drdurczok/3DPrinter/CAD/StencilParts/HotEnd.fcstd

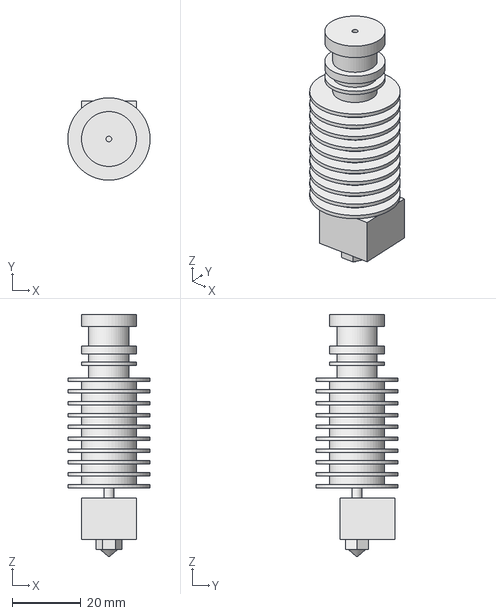
[picture p20: CAD file, 2017-04-10]
CAD/StencilParts/HotEnd.fcstd
24.0 x 24.0 x 70.5 mm
