drdurczok/3DPrinter/CAD/TopFrame/Corner_Bottom.fcstd

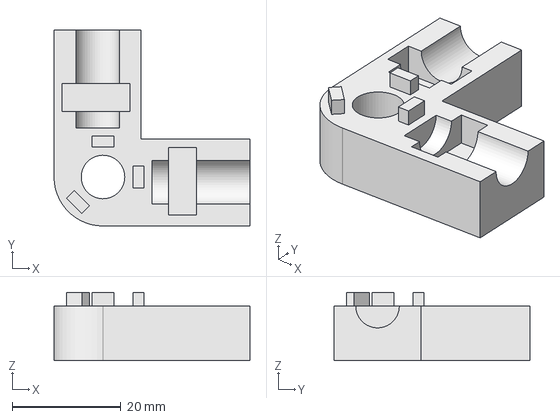
[picture p21: CAD file, 2017-05-19]
CAD/TopFrame/Corner_Bottom.fcstd
36.0 x 36.0 x 12.5 mm
