drdurczok/3DPrinter/CAD/X-Axis/HotEndMount.fcstd

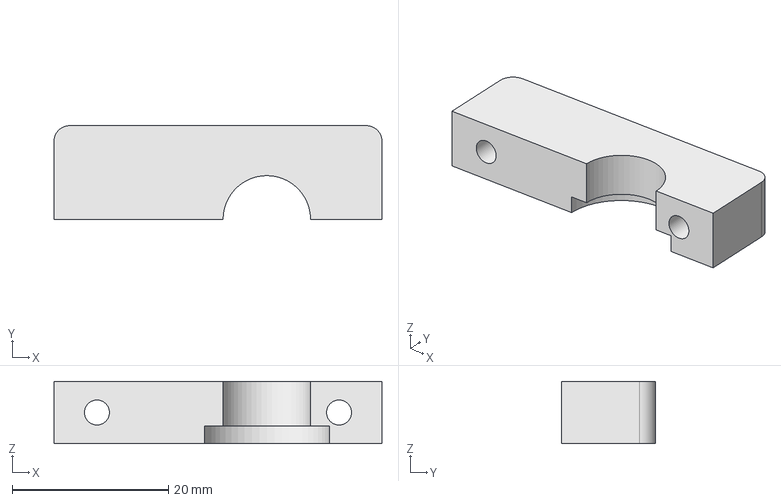
[picture p22: CAD file, 2017-05-19]
CAD/X-Axis/HotEndMount.fcstd
42.0 x 12.0 x 8.00 mm
