drdurczok/3DPrinter/CAD/Y-Axis/Y_MotorMount.fcstd

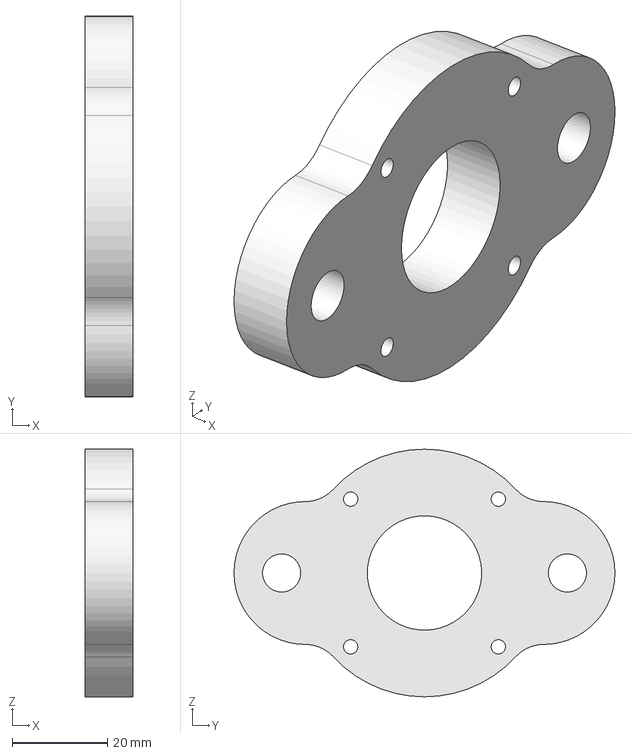
[picture p23: CAD file, 2017-05-19]
CAD/Y-Axis/Y_MotorMount.fcstd
10.0 x 80.0 x 52.0 mm
