drdurczok/3DPrinter/CAD/Z-Axis/Z-Axis_AxisMount.fcstd

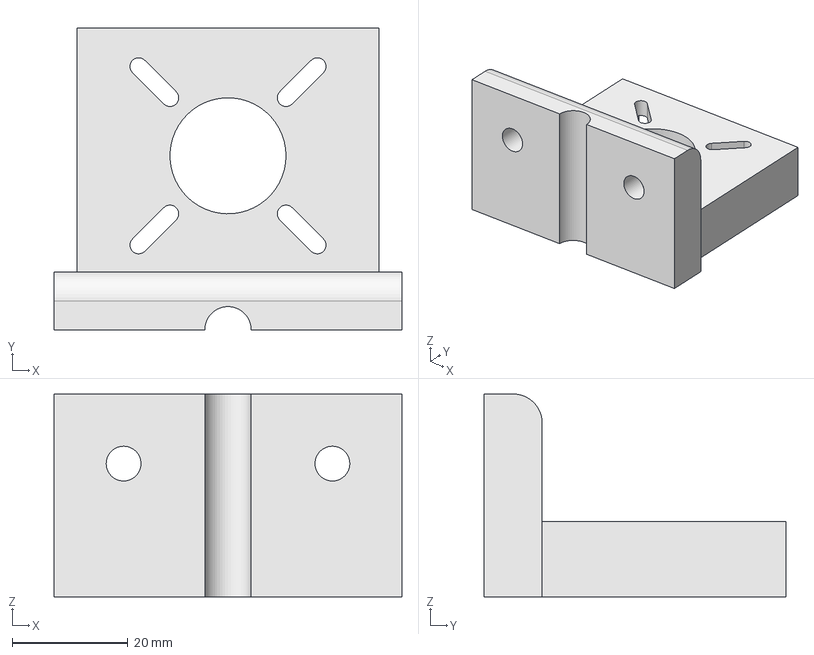
[picture p24: CAD file, 2017-04-15]
CAD/Z-Axis/Z-Axis_AxisMount.fcstd
60.0 x 52.0 x 35.0 mm
