drdurczok/3DPrinter/CAD/BottemFrame/board_shelf.fcstd

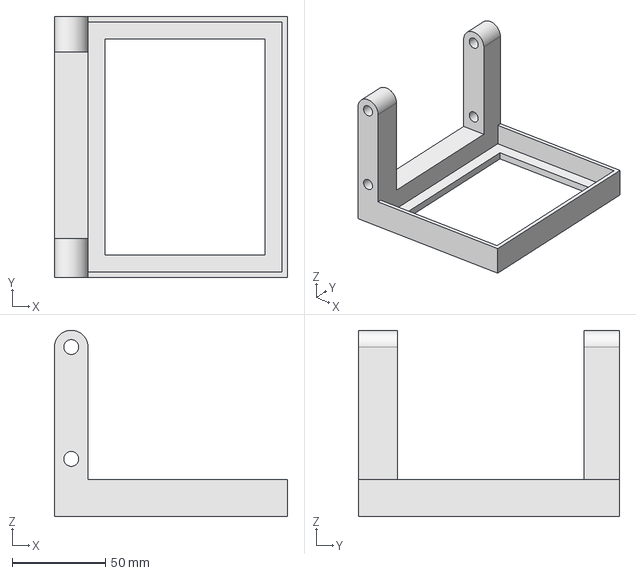
[picture p25: CAD file, 2017-05-19]
CAD/BottemFrame/board_shelf.fcstd
125.0 x 140.0 x 100.0 mm
