drdurczok/3DPrinter/CAD/PrintingBed/SGB_BearingMounts.fcstd

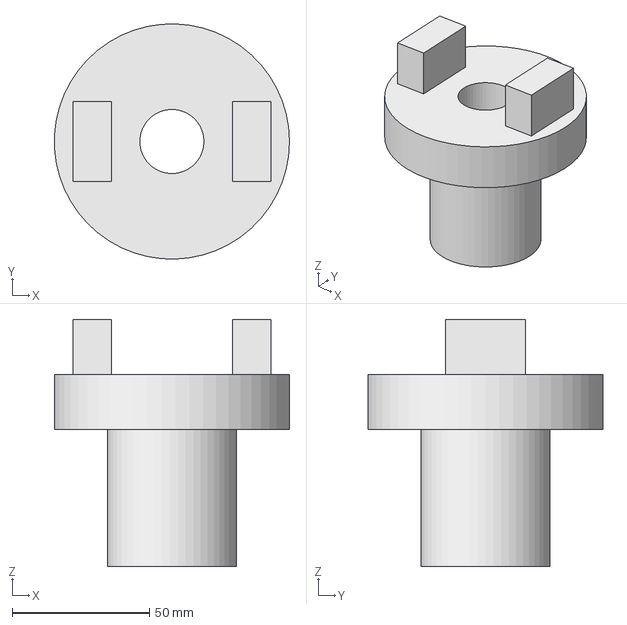
[picture p26: CAD file, 2017-03-07]
CAD/PrintingBed/SGB_BearingMounts.fcstd
85.5 x 85.6 x 90.0 mm
