drdurczok/3DPrinter/CAD/StencilParts/Nema17.fcstd

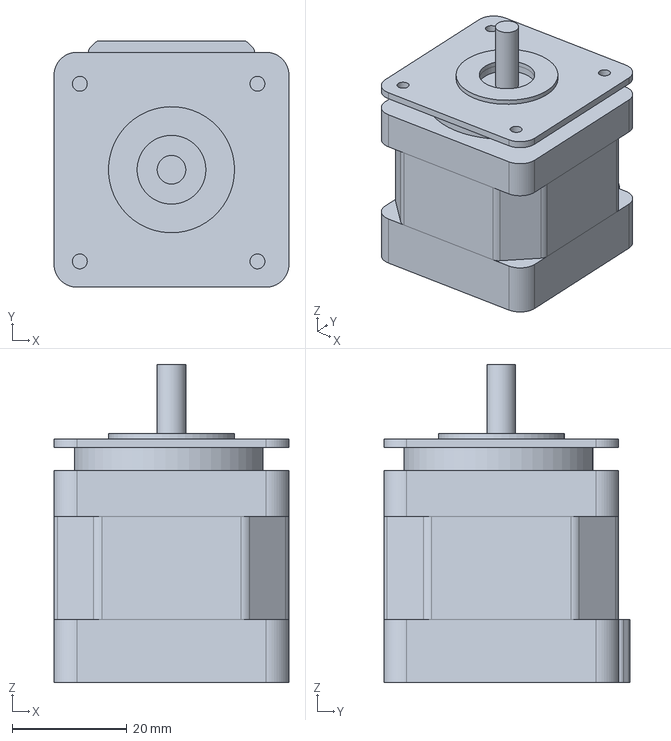
[picture p27: CAD file, 2017-04-10]
CAD/StencilParts/Nema17.fcstd
41.0 x 43.0 x 55.5 mm
