drdurczok/3DPrinter/CAD/TopFrame/Corner_Top.fcstd

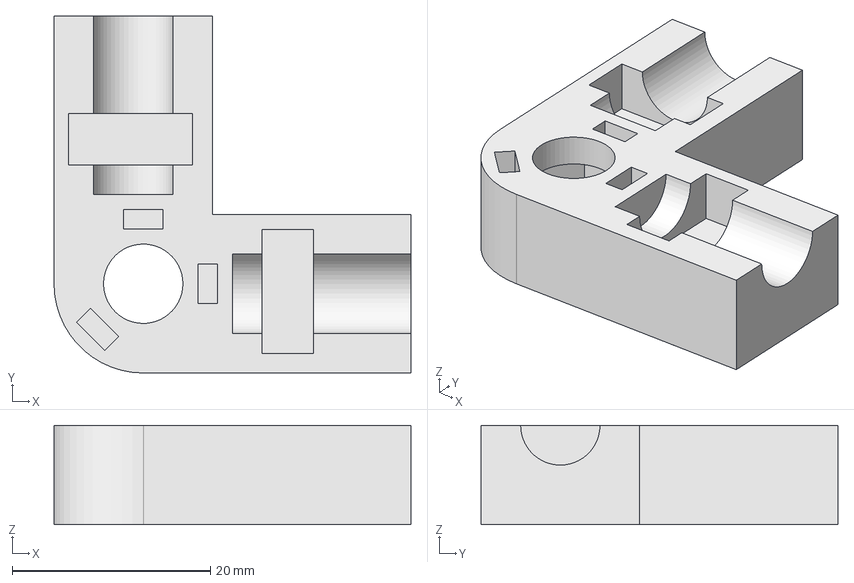
[picture p28: CAD file, 2017-05-19]
CAD/TopFrame/Corner_Top.fcstd
36.0 x 36.0 x 10.0 mm
