drdurczok/3DPrinter/CAD/X-Axis.fcstd

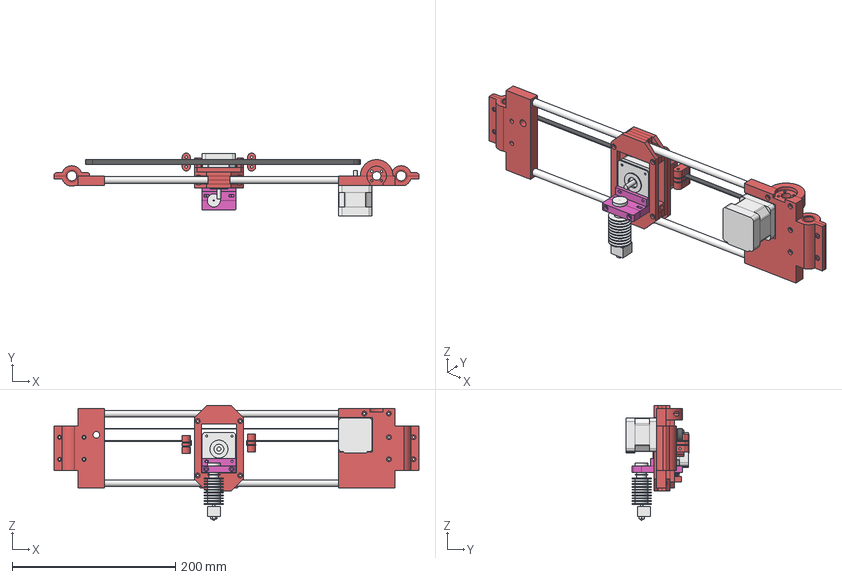
[picture p29: CAD file, 2017-05-19]
CAD/X-Axis.fcstd
446.7 x 77.0 x 141.0 mm
Nema17
Nema17_X
Belt
Spring
HotEnd
X-Rods
Shoulders
HotEndMount001
X-Carrage
