drdurczok/3DPrinter/CAD/X-Axis/X-Carrage_Back.fcstd

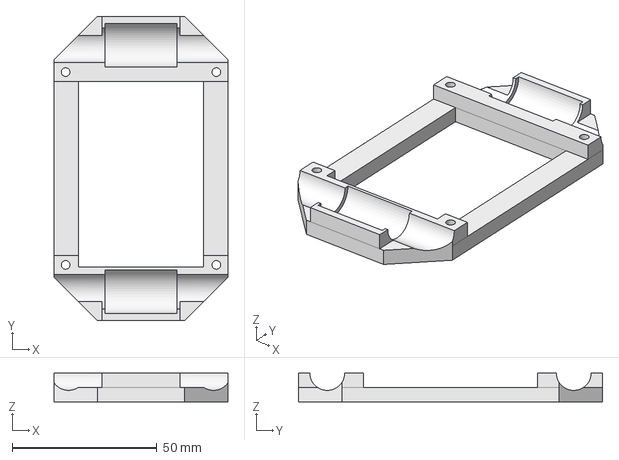
[picture p30: CAD file, 2017-05-19]
CAD/X-Axis/X-Carrage_Back.fcstd
60.0 x 105.0 x 10.0 mm
