drdurczok/3DPrinter/CAD/Y-Axis/HeightKnob.fcstd

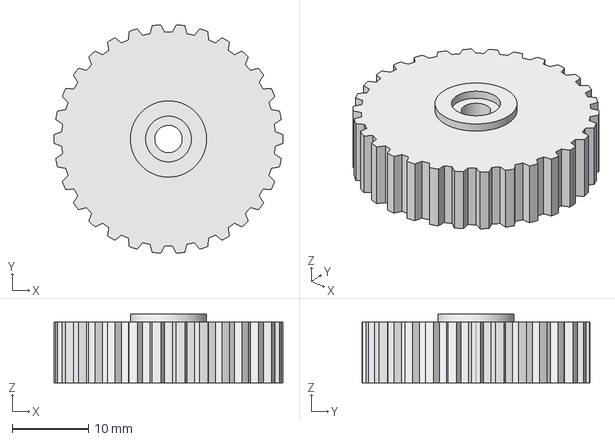
[picture p31: CAD file, 2017-04-24]
CAD/Y-Axis/HeightKnob.fcstd
30.0 x 29.9 x 9.00 mm
