drdurczok/3DPrinter/CAD/Z-Axis/Z-Axis_FrameMount.fcstd

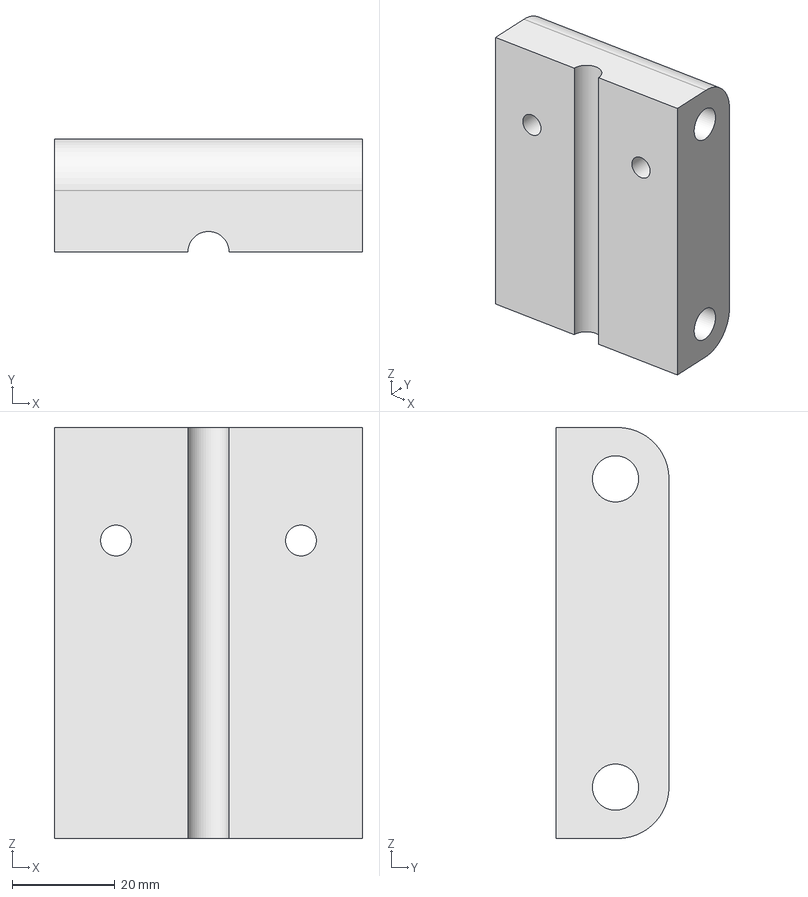
[picture p32: CAD file, 2017-04-15]
CAD/Z-Axis/Z-Axis_FrameMount.fcstd
60.0 x 22.0 x 80.0 mm
