drdurczok/3DPrinter/CAD/PrintingBed/ServoGearBox.fcstd

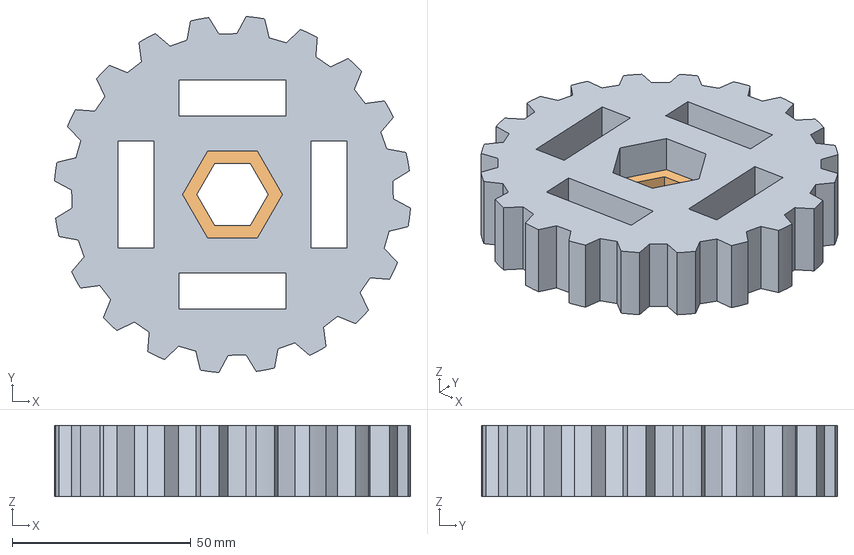
[picture p33: CAD file, 2017-03-07]
CAD/PrintingBed/ServoGearBox.fcstd
99.7 x 99.7 x 20.0 mm
NutPad
NutBreak
