drdurczok/3DPrinter/CAD/StencilParts/SmoothRod380mm.fcstd

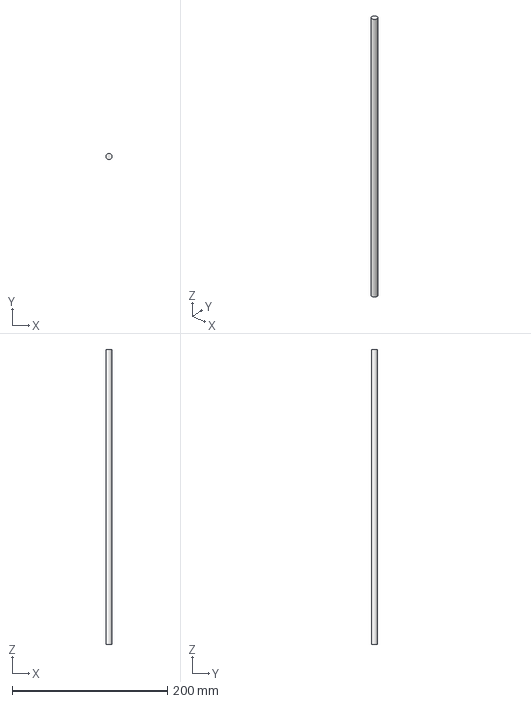
[picture p34: CAD file, 2017-04-02]
CAD/StencilParts/SmoothRod380mm.fcstd
7.99 x 8.00 x 380.0 mm
