drdurczok/3DPrinter/CAD/STP/Peripheral.step

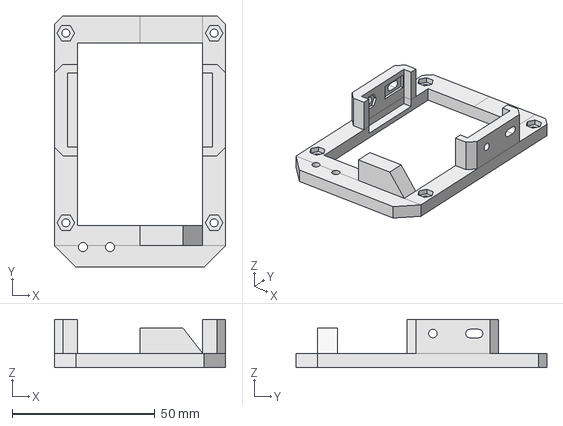
[picture p35: CAD file, 2017-05-19]
CAD/STP/Peripheral.step
60.0 x 88.0 x 17.0 mm
