drdurczok/3DPrinter/CAD/Y-Axis.fcstd

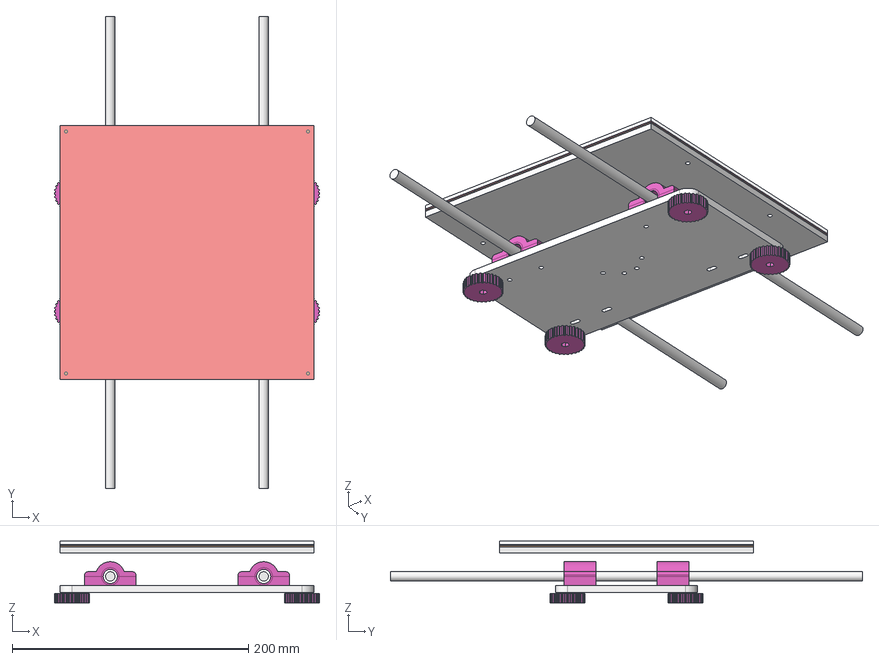
[picture p36: CAD file, 2017-04-24]
CAD/Y-Axis.fcstd
225.0 x 400.0 x 52.5 mm
Rods
Y-Base
BearingMount
PrintingBedBase
Insulation
HeatBed
GlassPrintingBed
HeightKnob
