drdurczok/3DPrinter/CAD/Y-Axis/SingleLinearBearingBASE.fcstd

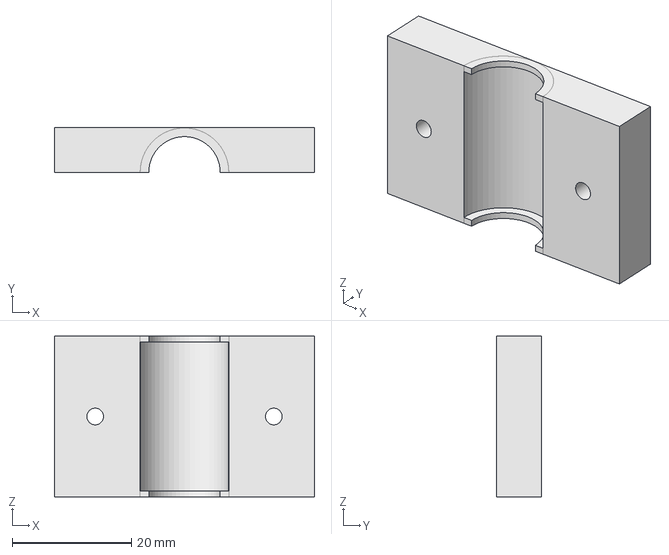
[picture p37: CAD file, 2017-04-24]
CAD/Y-Axis/SingleLinearBearingBASE.fcstd
43.7 x 7.50 x 27.0 mm
