drdurczok/3DPrinter/CAD/Frame.fcstd

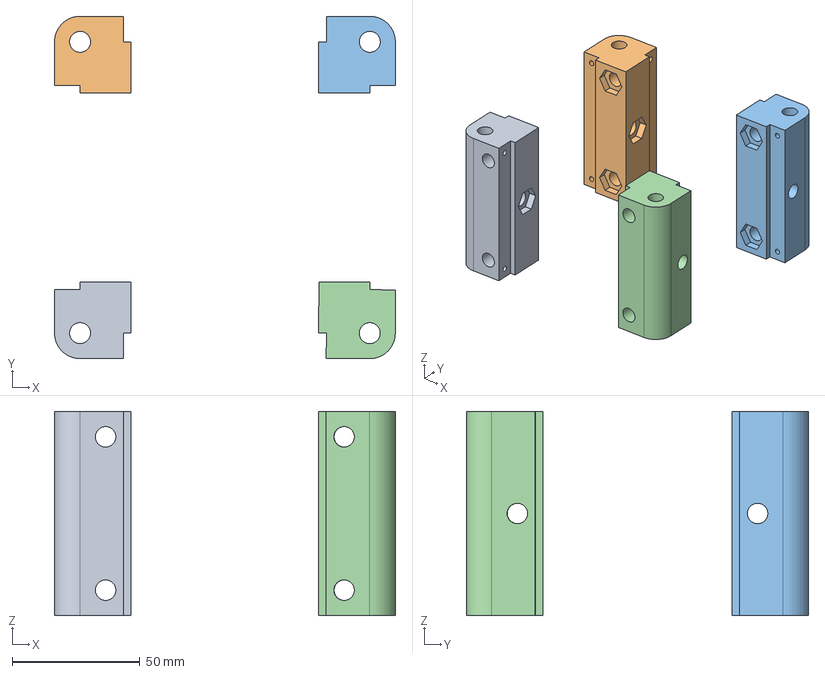
[picture p38: CAD file, 2017-04-10]
CAD/Frame.fcstd
133.4 x 134.0 x 80.0 mm
Corner_FL
Corner_BL
Corner_BR
Corner_FR
