drdurczok/3DPrinter/CAD/PrintingBed/SGH_BearingCup.fcstd

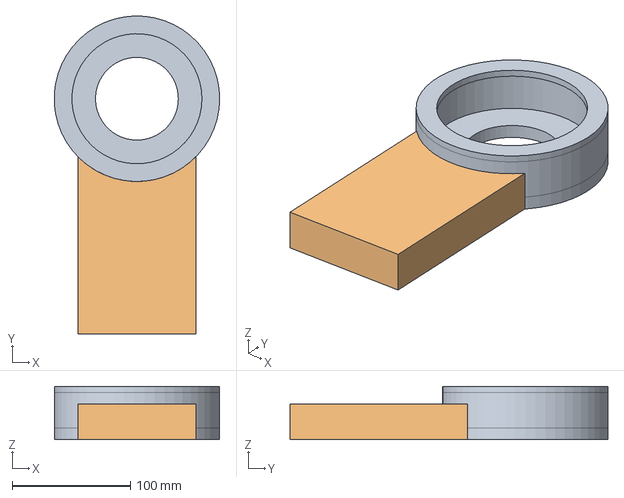
[picture p39: CAD file, 2017-03-07]
CAD/PrintingBed/SGH_BearingCup.fcstd
139.9 x 269.0 x 45.0 mm
BLock
BArm
