drdurczok/3DPrinter/CAD/StencilParts/SmoothRod406mm.fcstd

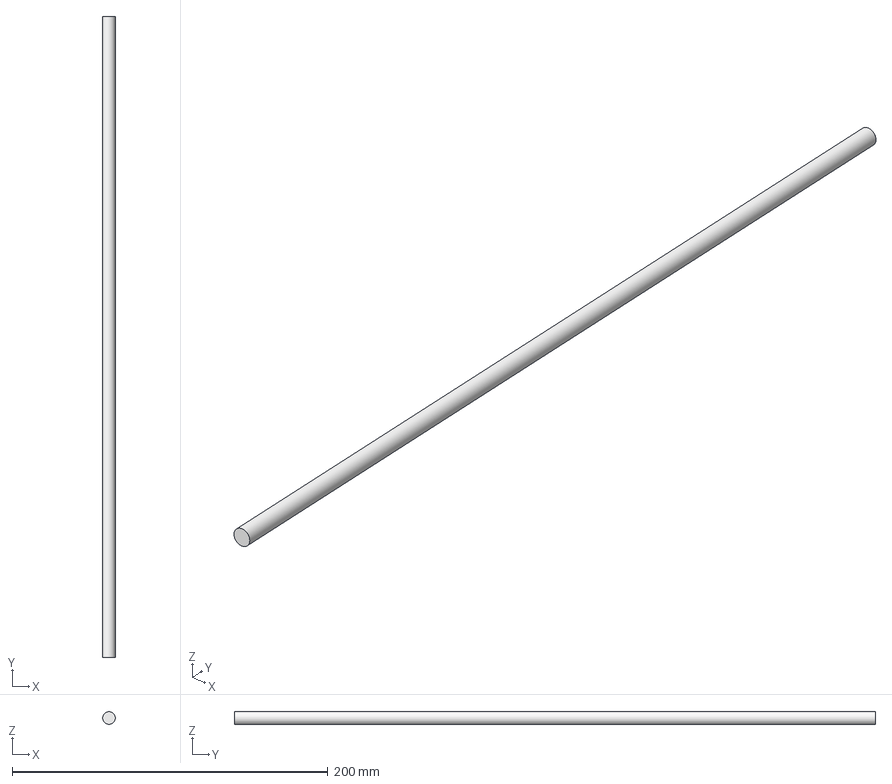
[picture p40: CAD file, 2017-04-02]
CAD/StencilParts/SmoothRod406mm.fcstd
7.99 x 406.0 x 8.00 mm
