drdurczok/3DPrinter/CAD/STP/ExtruderLever.step

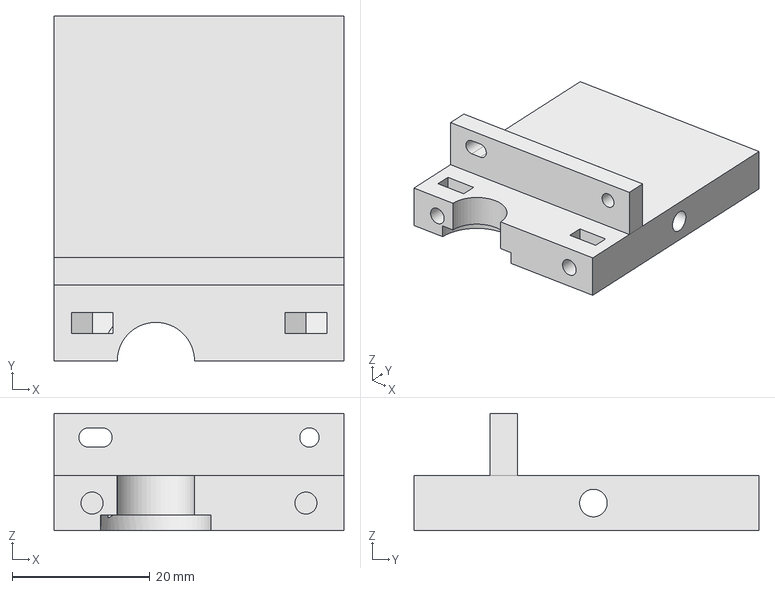
[picture p41: CAD file, 2017-05-19]
CAD/STP/ExtruderLever.step
42.0 x 50.0 x 17.0 mm
