drdurczok/3DPrinter/CAD/X-Axis/LeftShoulder.fcstd

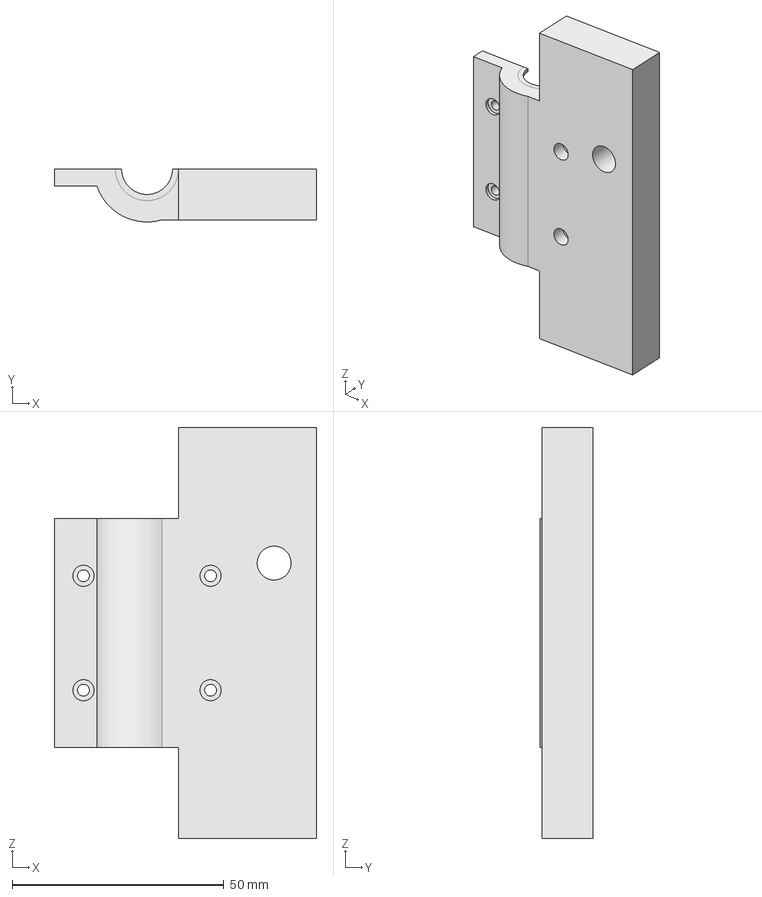
[picture p42: CAD file, 2017-05-19]
CAD/X-Axis/LeftShoulder.fcstd
61.8 x 12.5 x 97.0 mm
