drdurczok/3DPrinter/CAD/Y-Axis/SingleLinearBearingMount.fcstd

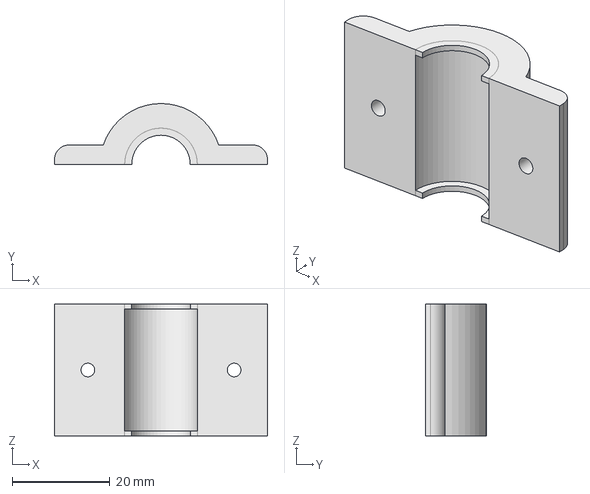
[picture p43: CAD file, 2017-04-24]
CAD/Y-Axis/SingleLinearBearingMount.fcstd
43.7 x 12.5 x 27.0 mm
