drdurczok/3DPrinter/CAD/StencilParts/SmoothRod310mm.fcstd

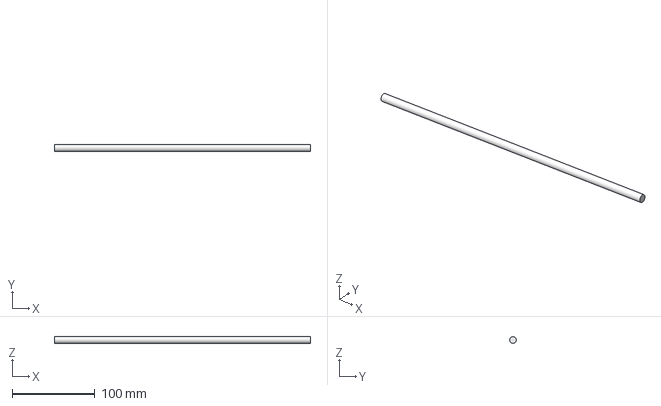
[picture p44: CAD file, 2017-04-02]
CAD/StencilParts/SmoothRod310mm.fcstd
310.0 x 7.99 x 8.00 mm
