drdurczok/3DPrinter/CAD/Y-Axis/BeltMount.fcstd

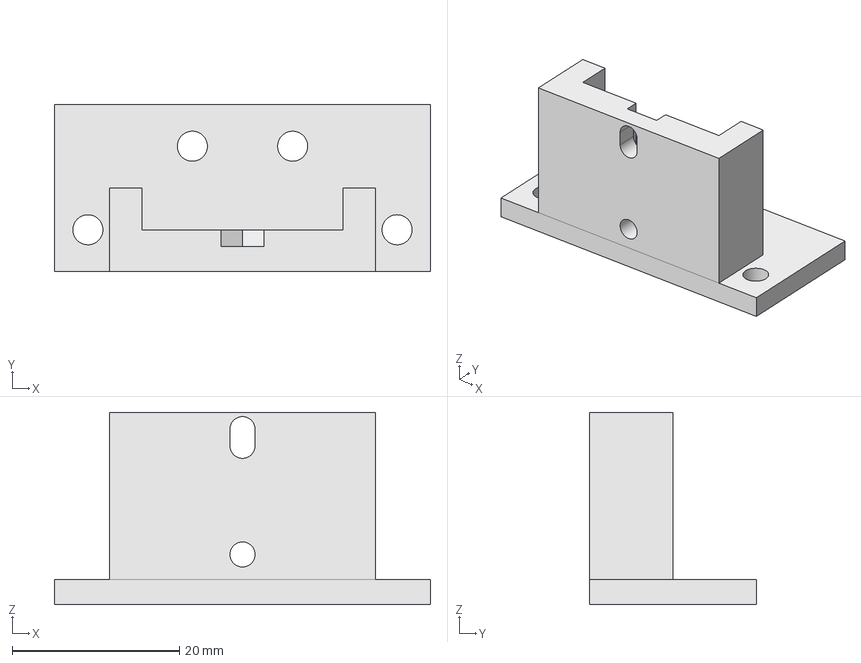
[picture p45: CAD file, 2017-04-24]
CAD/Y-Axis/BeltMount.fcstd
45.0 x 20.0 x 23.0 mm
