drdurczok/3DPrinter/CAD/StencilParts/BearingLodge.fcstd

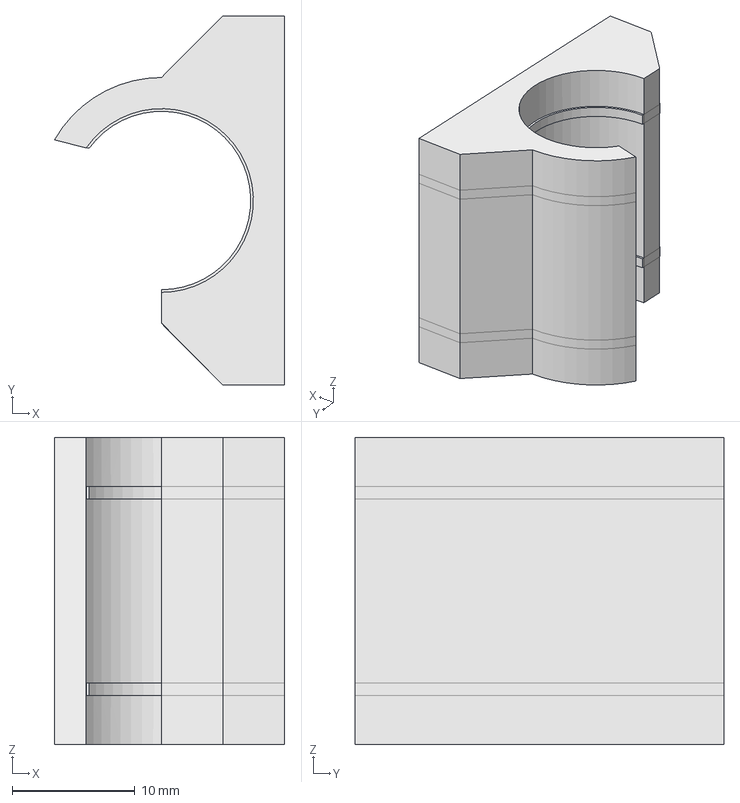
[picture p46: CAD file, 2017-03-17]
CAD/StencilParts/BearingLodge.fcstd
18.7 x 30.0 x 25.0 mm
