drdurczok/3DPrinter/CAD/Y-Axis/Y-Base.fcstd

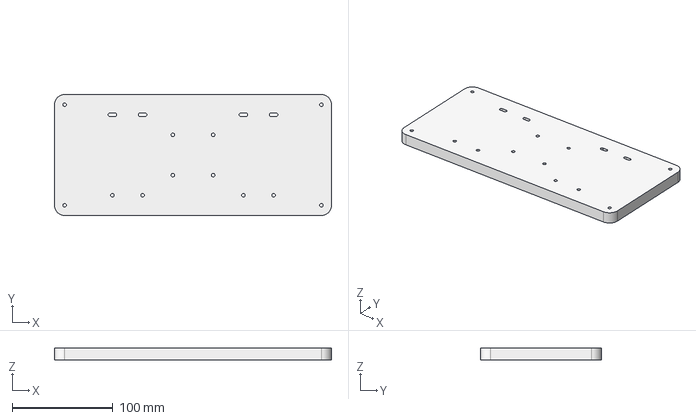
[picture p47: CAD file, 2017-04-24]
CAD/Y-Axis/Y-Base.fcstd
275.0 x 120.0 x 12.0 mm
