drdurczok/3DPrinter/CAD/X-Axis/BeltTensioner.fcstd

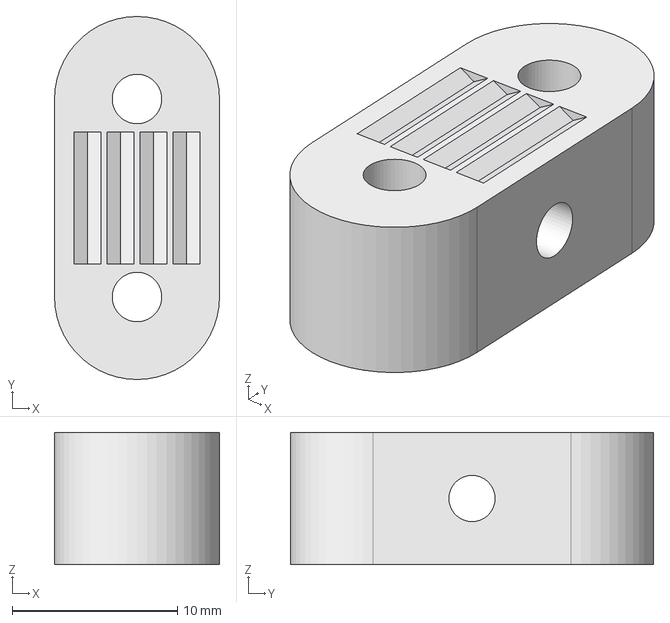
[picture p48: CAD file, 2017-04-10]
CAD/X-Axis/BeltTensioner.fcstd
10.0 x 22.0 x 8.00 mm
