drdurczok/3DPrinter/CAD/X-Axis/DoubleLinearBearingMount.fcstd

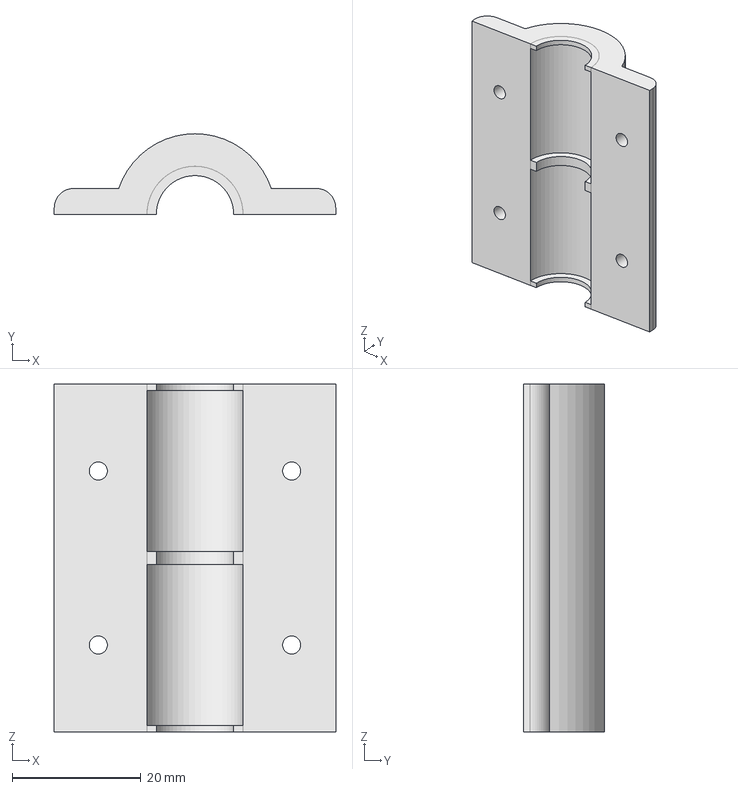
[picture p49: CAD file, 2017-04-10]
CAD/X-Axis/DoubleLinearBearingMount.fcstd
43.7 x 12.5 x 54.0 mm
