drdurczok/3DPrinter/CAD/X-Axis/BeltClip.fcstd

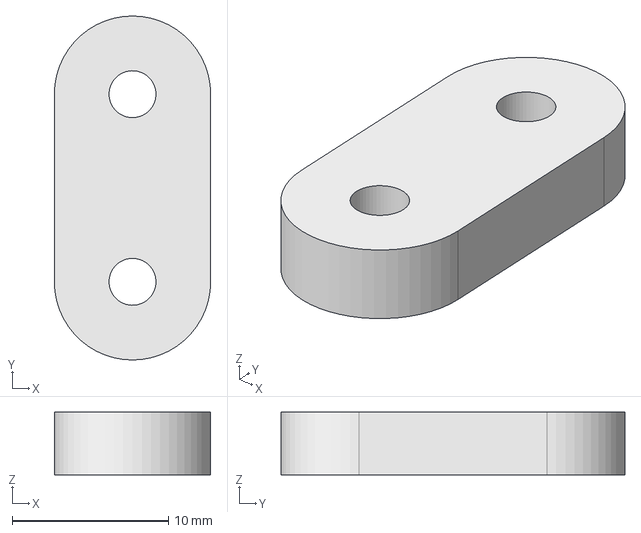
[picture p50: CAD file, 2017-04-10]
CAD/X-Axis/BeltClip.fcstd
10.0 x 22.0 x 4.00 mm
