drdurczok/3DPrinter/Technical Drawings/PDF/RightShoulder_A.pdf

# Ra3.2Ra5

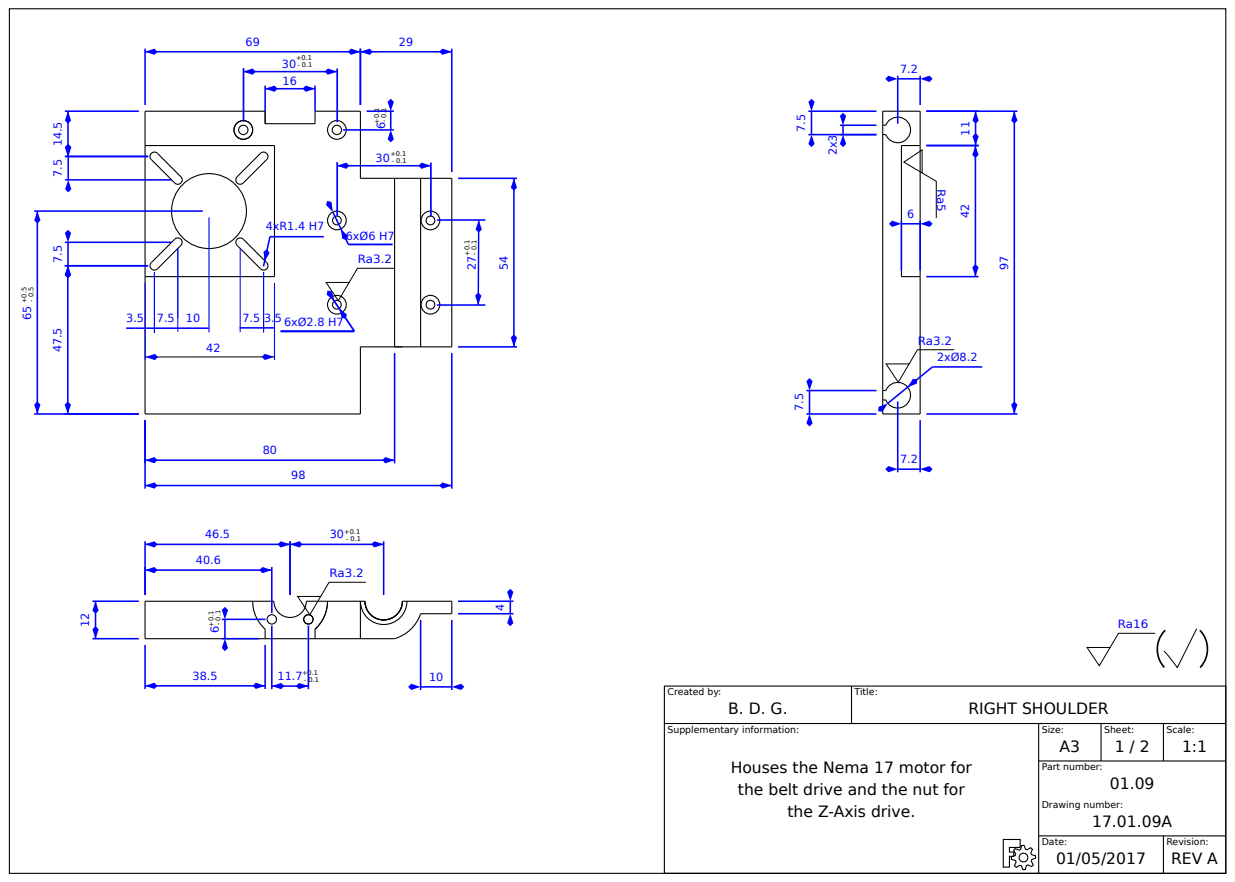
[picture p61: page 1]
Created by:; Title:; Supplementary information:; Size:; Sheet:; Scale:; Part number:; Drawing number:; Date:; Revision:; RIGHT SHOULDER; REV A

Houses the Nema 17 motor for
the belt drive and the nut for
the Z-Axis drive.
