drdurczok/3DPrinter/Technical Drawings/PDF/X-Axis.pdf

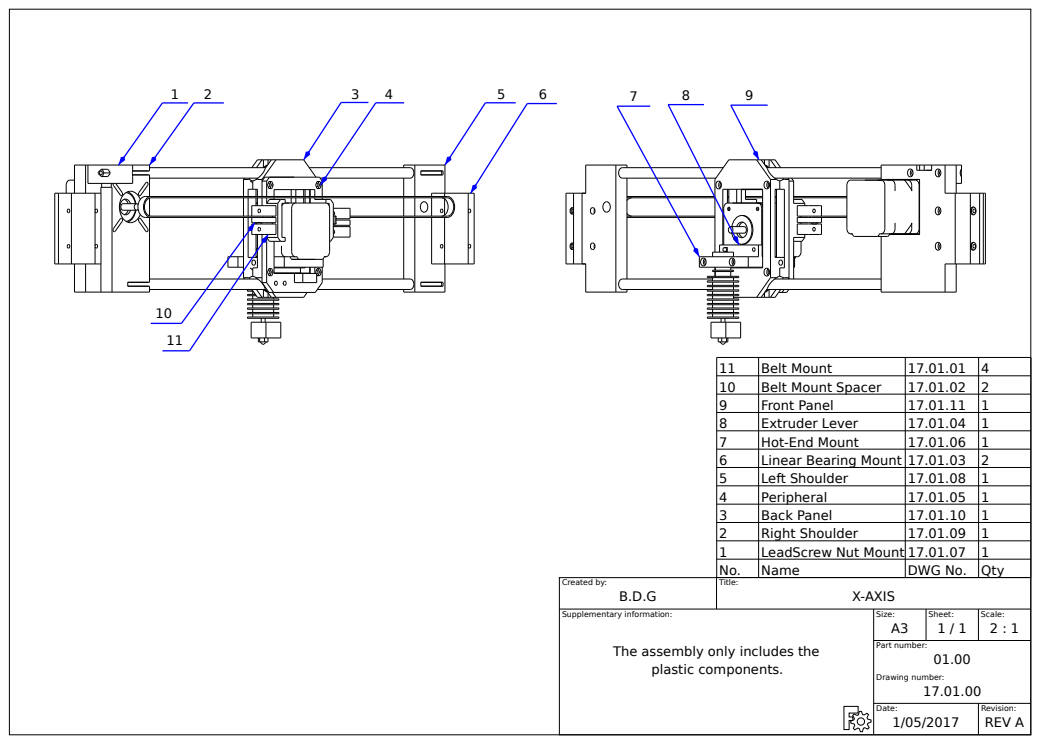
[picture p62: page 1]
Created by:; Title:; Supplementary information:; Size:; Sheet:; Scale:; Part number:; Drawing number:; Date:; Revision:; X-AXIS; REV A

11 | Belt Mount | 17.01.01 | 4
10 | Belt Mount Spacer | 17.01.02 | 2
9 | Front Panel | 17.01.11 | 1
8 | Extruder Lever | 17.01.04 | 1
7 | Hot-End Mount | 17.01.06 | 1
6 | Linear Bearing Mount | 17.01.03 | 2
5 | Left Shoulder | 17.01.08 | 1
4 | Peripheral | 17.01.05 | 1
3 | Back Panel | 17.01.10 | 1
2 | Right Shoulder | 17.01.09 | 1
1 | LeadScrew Nut Mount 17.01.07 | | 1
No. | Name | DWG No. | Qty

The assembly only includes the
plastic components.
