drdurczok/3DPrinter/Technical Drawings/PDF/X-Carrage(Back).pdf

## Ra5Ra5

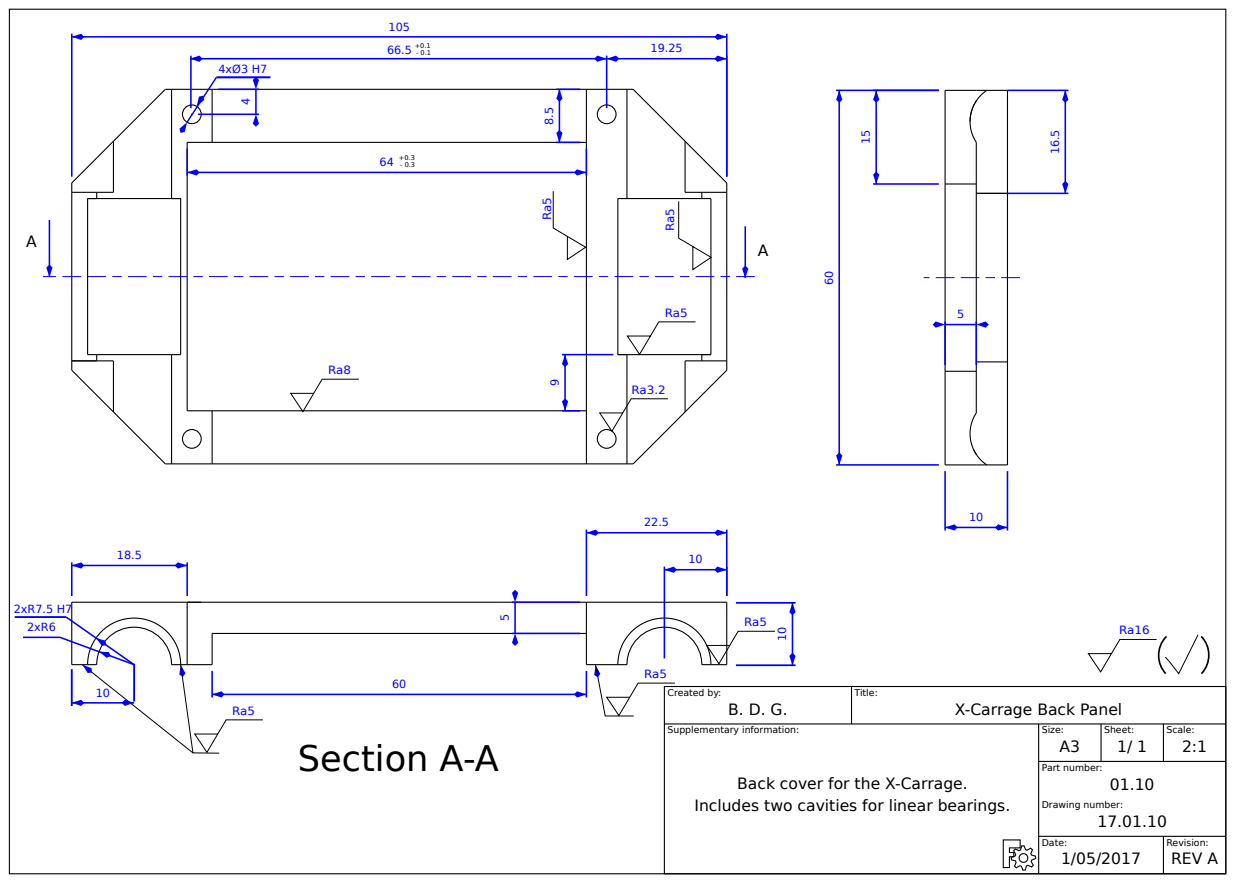
[picture p63: page 1]
Created by:; Title:; Supplementary information:; Size:; Sheet:; Scale:; Part number:; Drawing number:; Date:; Revision:; X-Carrage Back Panel; REV A; Section A-A

Back cover for the X-Carrage.
Includes two cavities for linear bearings.
