drdurczok/3DPrinter/Technical Drawings/PDF/X-Carrage(Front).pdf

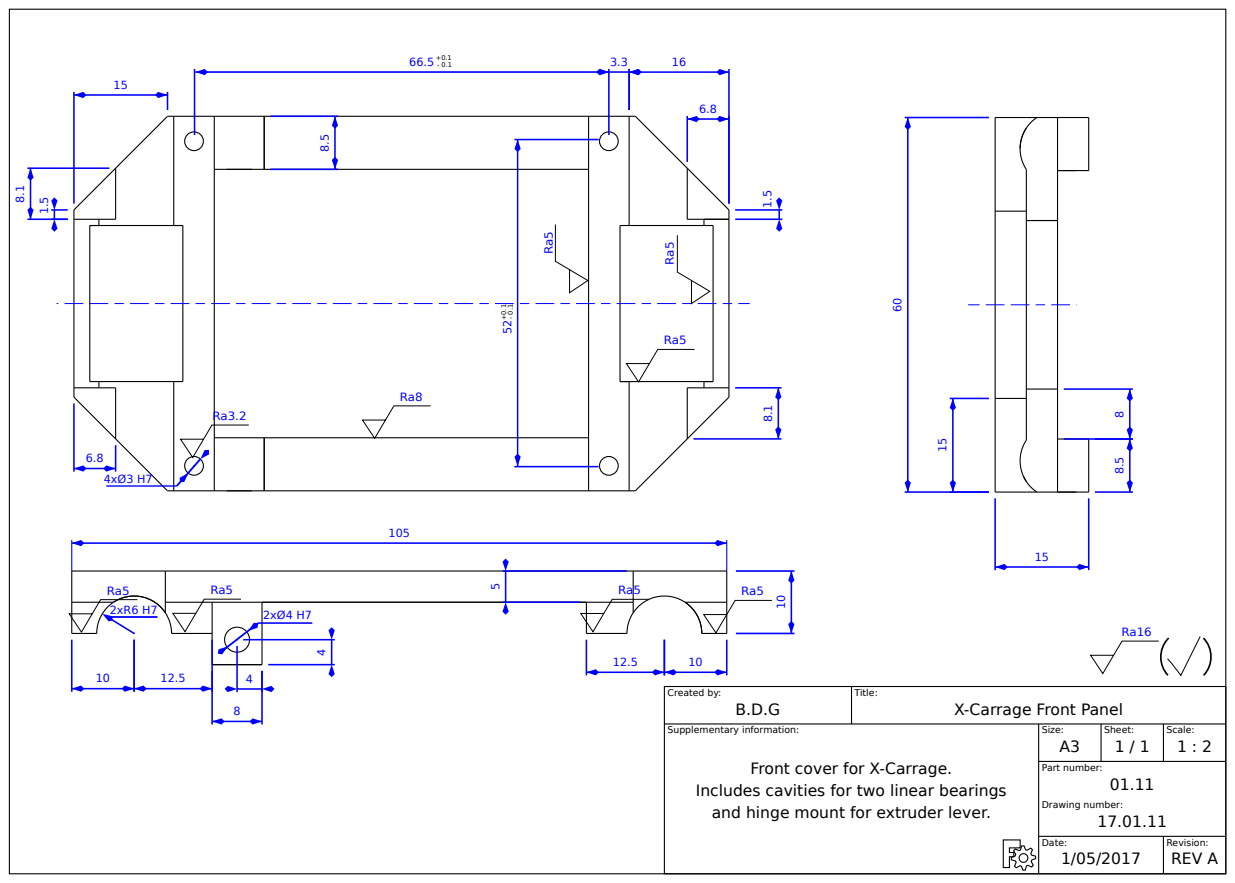
[picture p64: page 1]
Created by:; Title:; Supplementary information:; Size:; Sheet:; Scale:; Part number:; Drawing number:; Date:; Revision:; X-Carrage Front Panel; REV A

Front cover for X-Carrage.

Includes cavities for two linear bearings
and hinge mount for extruder lever.
