drdurczok/3DPrinter/Technical Drawings/PDF/Y-Axis.pdf

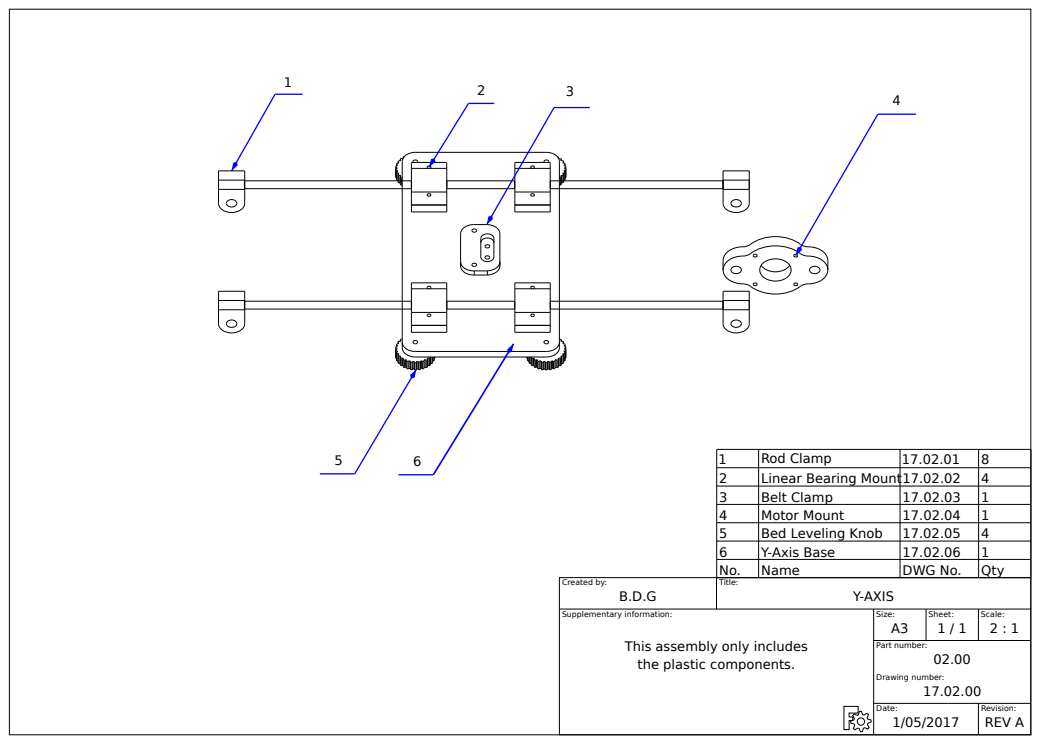
[picture p65: page 1]
Created by:; Title:; Supplementary information:; Size:; Sheet:; Scale:; Part number:; Drawing number:; Date:; Revision:; Y-AXIS; REV A; Rod Clamp

2 | Linear Bearing Mount17.02.02 | | 4
3 | Belt Clamp | 17.02.03 | 1
4 | Motor Mount | 17.02.04 | 1
5 | Bed Leveling Knob | 17.02.05 | 4
6 | Y-Axis Base | 17.02.06 | 1
No. | Name | DWG No. | Qty

This assembly only includes
the plastic components.
